gnimm/neuromime/1.0.1_minor_corrections_post_MUTEK/sketches_notes/oldboard.jpg

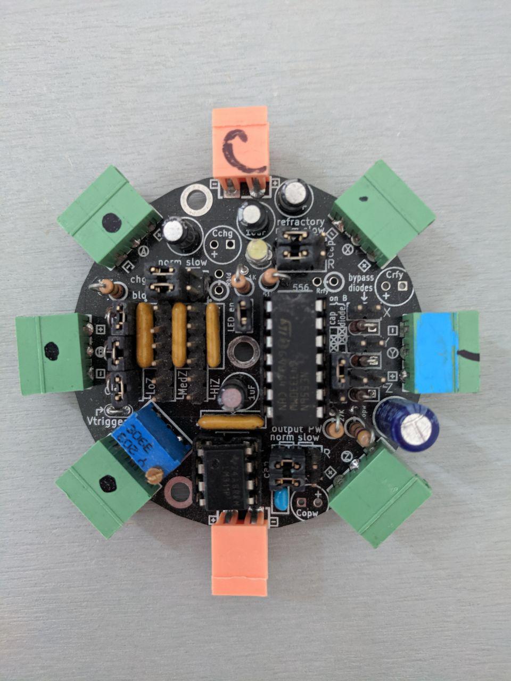
1.0.1_minor_corrections_post_MUTEK/sketches_notes/oldboard.jpg
