gnimm/neuromime/1.0.1_minor_corrections_post_MUTEK/sketches_notes/signal-attachment.jpeg

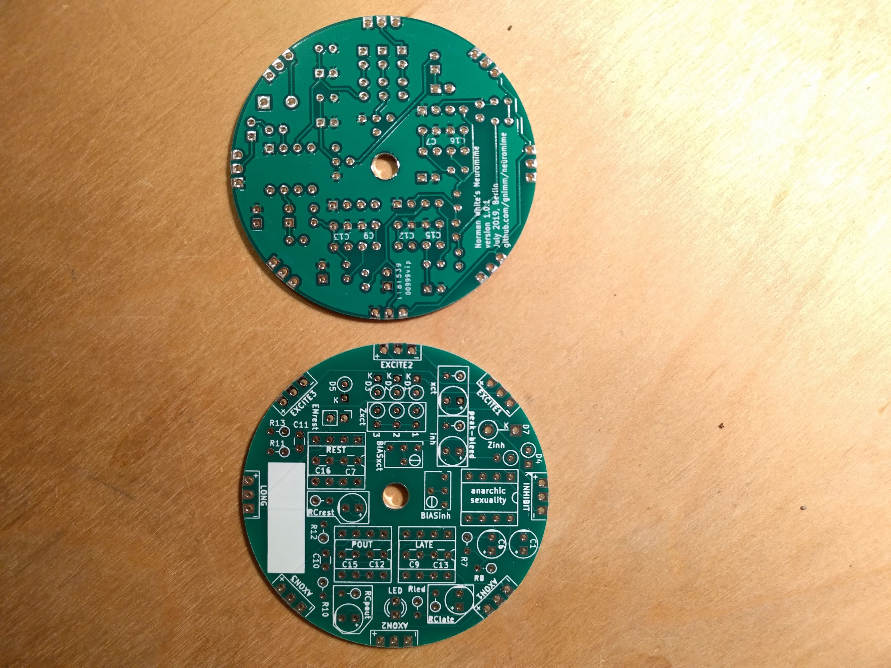
1.0.1_minor_corrections_post_MUTEK/sketches_notes/signal-attachment.jpeg
