gnimm/neuromime/ref/Neuromime_finished_board_ver_1.0.0.png

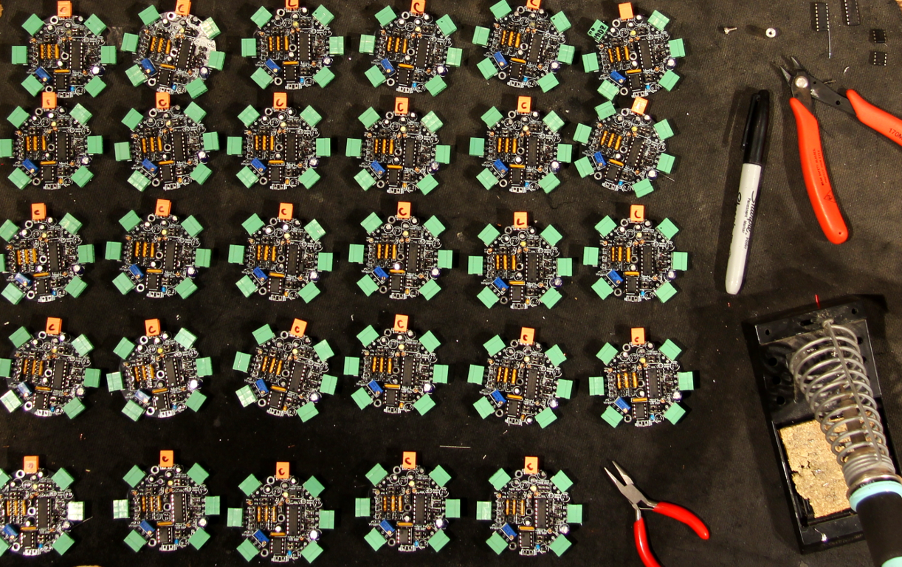
ref/Neuromime_finished_board_ver_1.0.0.png
