gnimm/neuromime/1.0.1/project_files/neuromime_1.0.1.sch

## KiCad design 1.0.1/project_files/neuromime_1.0.1.sch (2019-07-09)

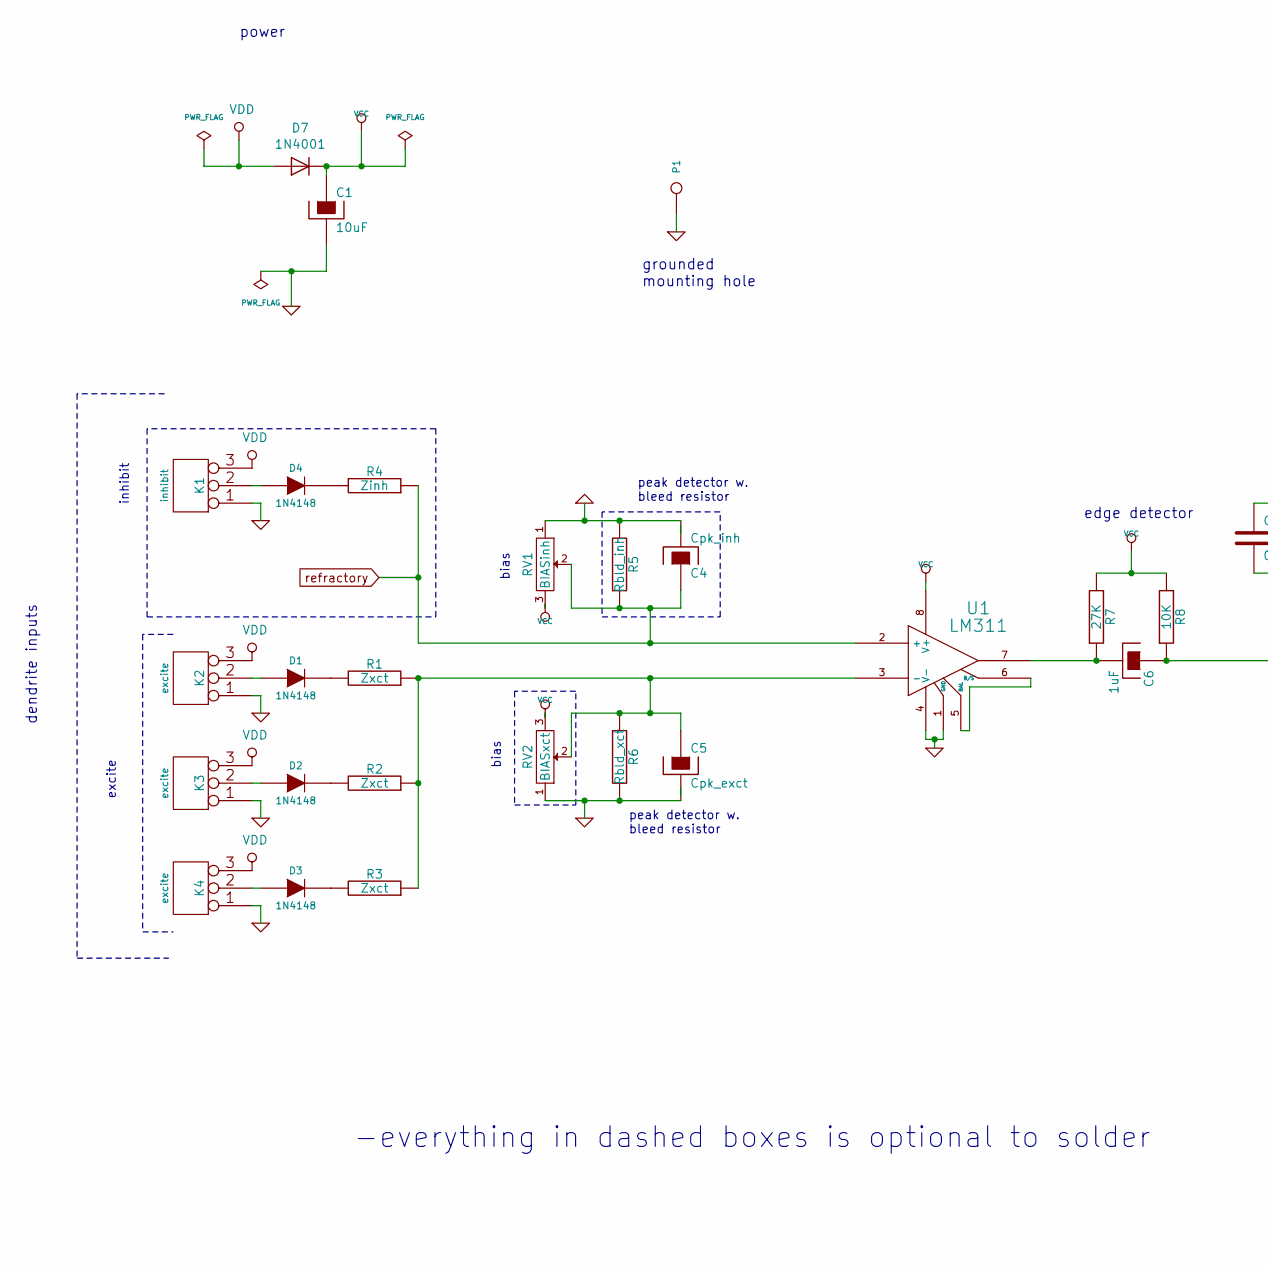
[picture p19: schematic neuromime_1.0.1.sch, part in row 1, column 1]

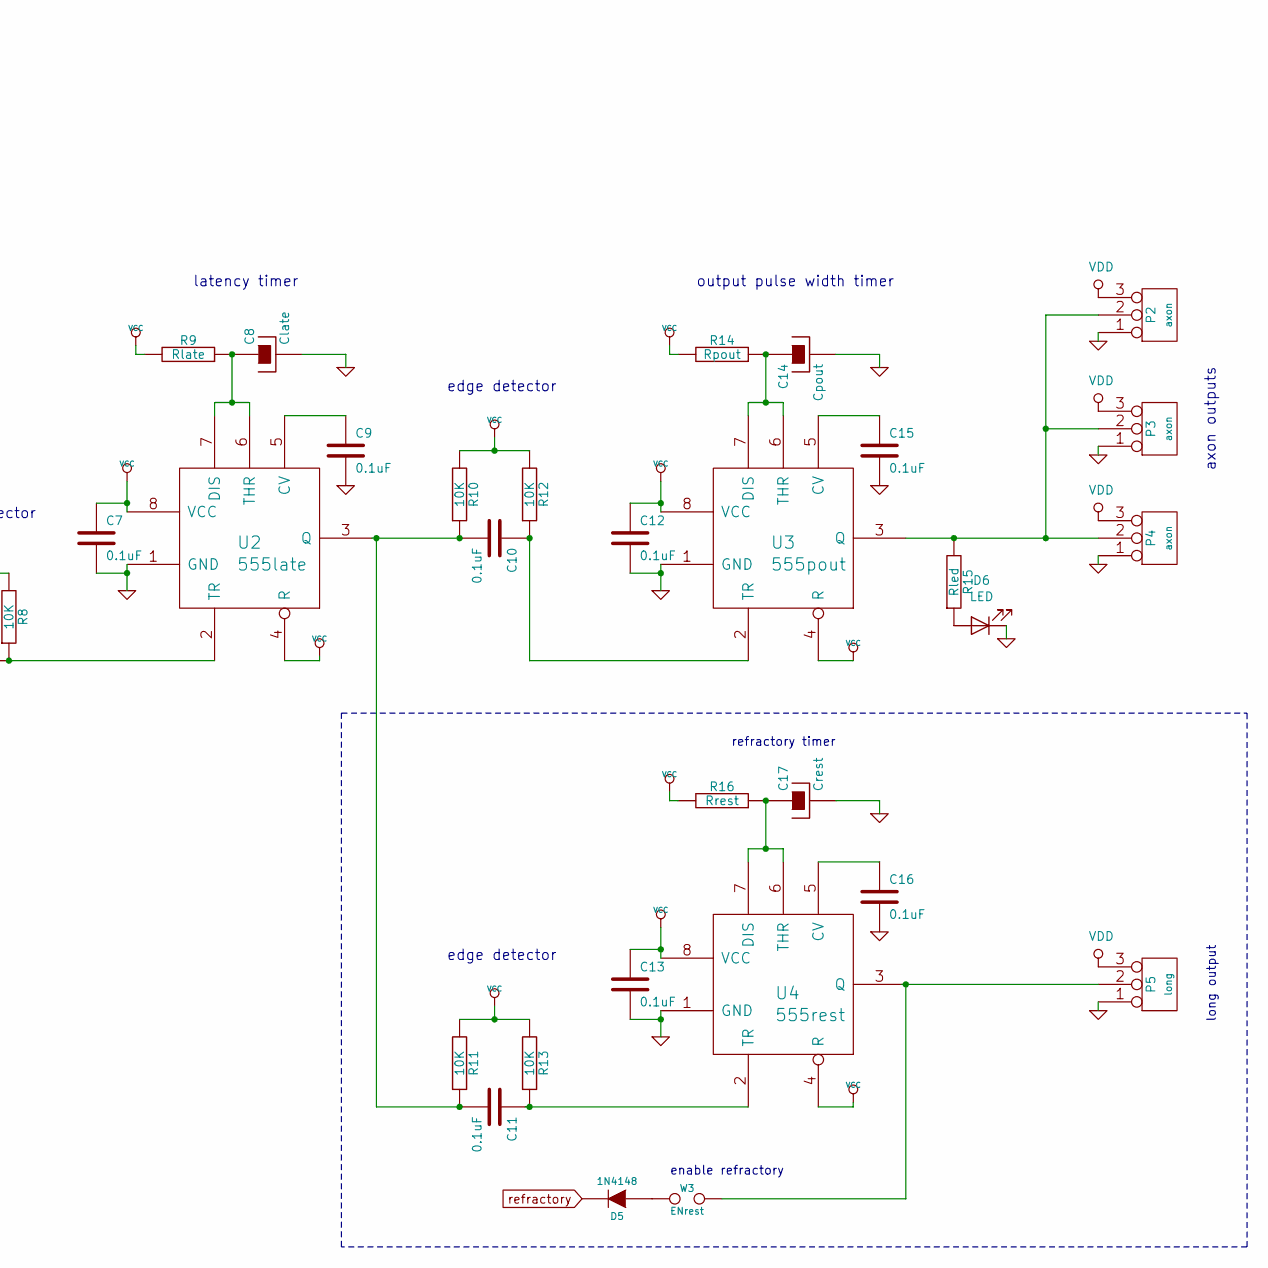
[picture p20: schematic neuromime_1.0.1.sch, part in row 1, column 2]

Parts:
C1: 10uF; CP_Radial_D5.0mm_P2.50mm_positive_symbol_inside
C4: Cpk_inh; CP_Radial_D5.0mm_P2.50mm_positive_symbol_inside
C5: Cpk_exct; CP_Radial_D5.0mm_P2.50mm_positive_symbol_inside
C6: 1uF; CP_Radial_D5.0mm_P2.50mm_positive_symbol_inside
C7, C9, C10, C11, C12, C13, C15, C16: 0.1uF; C_Disc_D3.0mm_W1.6mm_P2.50mm
C8: Clate; CP_Radial_D5.0mm_P2.50mm_positive_symbol_inside
C14: Cpout; CP_Radial_D5.0mm_P2.50mm_positive_symbol_inside_single_corr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
C17: Crest; CP_Radial_D5.0mm_P2.50mm_positive_symbol_inside
D1, D2, D3, D4, D5: 1N4148; D_DO-35_SOD27_P2.54mm_Vertical_KathodeUp
D6: LED; LED_D3.0mm
D7: 1N4001; D_DO-41_SOD81_P5.08mm_Vertical_KathodeUp
K1: inhibit; PinSocket_1x03_P2.54mm_Horizontal_elongated
K2, K3, K4: excite; PinSocket_1x03_P2.54mm_Horizontal_elongated
P1: mnt; MountingHole_4.5mm_PTH
P2, P3, P4: axon; PinHeader_1x03_P2.54mm_Horizontal_elomgated_pads
P5: long; PinHeader_1x03_P2.54mm_Horizontal_elomgated_pads
R1, R2, R3: Zxct; R_Axial_DIN0207_L6.3mm_D2.5mm_P2.54mm_Vertical_pad_numbers_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
R4: Zinh; R_Axial_DIN0207_L6.3mm_D2.5mm_P2.54mm_Vertical_pad_numbers_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
R5: Rbld_inh; R_Axial_DIN0204_L3.6mm_D1.6mm_P2.54mm_Vertical
R6: Rbld_xct; R_Axial_DIN0204_L3.6mm_D1.6mm_P2.54mm_Vertical
R7: 27K; R_Axial_DIN0204_L3.6mm_D1.6mm_P2.54mm_Vertical
R8, R10, R11, R12, R13: 10K; R_Axial_DIN0204_L3.6mm_D1.6mm_P2.54mm_Vertical
R9: Rlate; R_Axial_DIN0204_L3.6mm_D1.6mm_P2.54mm_Vertical
R14: Rpout; R_Axial_DIN0204_L3.6mm_D1.6mm_P2.54mm_Vertical
R15: Rled; R_Axial_DIN0204_L3.6mm_D1.6mm_P2.54mm_Vertical
R16: Rrest; R_Axial_DIN0204_L3.6mm_D1.6mm_P2.54mm_Vertical
RV1: BIASinh; Potentiometer_Bourns_3266W_Vertical_pin_variation
RV2: BIASxct; Potentiometer_Bourns_3266W_Vertical_pin_variation
U1: LM311; DIP-8_W7.62mm_Socket
U2: 555late; DIP-8_W7.62mm_Socket
U3: 555pout; DIP-8_W7.62mm_Socket
U4: 555rest; DIP-8_W7.62mm_Socket
W3: ENrest; PinHeader_1x02_P2.54mm_Vertical

Connections:
GND: C1.2, C4.2, C5.2, C7.2, C8.2, C9.2, C12.2, C13.2, C14.2, C15.2, C16.2, C17.2, D6.1 (K), K1.1, K2.1, K3.1, K4.1, P1.1, P2.1, P3.1, P4.1, P5.1, R5.2, R6.2, RV1.1, RV2.1, U1.1 (GND), U1.4 (V-), U2.1 (GND), U3.1 (GND), U4.1 (GND)
unnamed: C5.1, R1.1, R2.1, R3.1, R6.1, RV2.2, U1.3 (-)
unnamed: C6.1, R8.1, U2.2 (TR)
unnamed: C6.2, R7.1, U1.7
unnamed: C8.1, R9.1, U2.6 (THR), U2.7 (DIS)
unnamed: C9.1, U2.5 (CV)
unnamed: C10.1, R12.1, U3.2 (TR)
unnamed: C10.2, C11.2, R10.1, R11.1, U2.3 (Q)
unnamed: C11.1, R13.1, U4.2 (TR)
unnamed: C14.1, R14.1, U3.6 (THR), U3.7 (DIS)
unnamed: C15.1, U3.5 (CV)
unnamed: C16.1, U4.5 (CV)
unnamed: C17.1, R16.1, U4.6 (THR), U4.7 (DIS)
unnamed: D1.1 (A), K2.2 (PM)
unnamed: D1.2 (K), R1.2
unnamed: D2.1 (A), K3.2 (PM)
unnamed: D2.2 (K), R2.2
unnamed: D3.1 (A), K4.2 (PM)
unnamed: D3.2 (K), R3.2
unnamed: D4.1 (A), K1.2 (PM)
unnamed: D4.2 (K), R4.2
unnamed: D5.1 (A), W3.1
unnamed: D6.2 (A), R15.1
unnamed: P2.2 (PM), P3.2 (PM), P4.2 (PM), R15.2, U3.3 (Q)
unnamed: P5.2 (PM), U4.3 (Q), W3.2
unnamed: U1.5 (BAL), U1.6 (B/S)
VCC: C1.1, C7.1, C12.1, C13.1, D7.1 (K), R7.2, R8.2, R9.2, R10.2, R11.2, R12.2, R13.2, R14.2, R16.2, RV1.3, RV2.3, U1.8 (V+), U2.4 (R), U2.8 (VCC), U3.4 (R), U3.8 (VCC), U4.4 (R), U4.8 (VCC)
VDD: D7.2 (A), K1.3, K2.3, K3.3, K4.3, P2.3, P3.3, P4.3, P5.3
refractory: C4.1, D5.2 (K), R4.1, R5.1, RV1.2, U1.2 (+)

Notes on the sheet:
grounded mounting hole
dendrite inputs
axon outputs
power
edge detector
output pulse width timer
latency timer
inhibit
excite
bias
peak detector w. bleed resistor
enable refractory
refractory timer
long output
-everything in dashed boxes is optional to solder
