gnimm/neuromime/1.0.0/project_files/rescue-backup/neuromime_1.0.0-2019-07-08-18-24-22.sch

## KiCad design 1.0.0/project_files/rescue-backup/neuromime_1.0.0-2019-07-08-18-24-22.sch (2015-03-06)

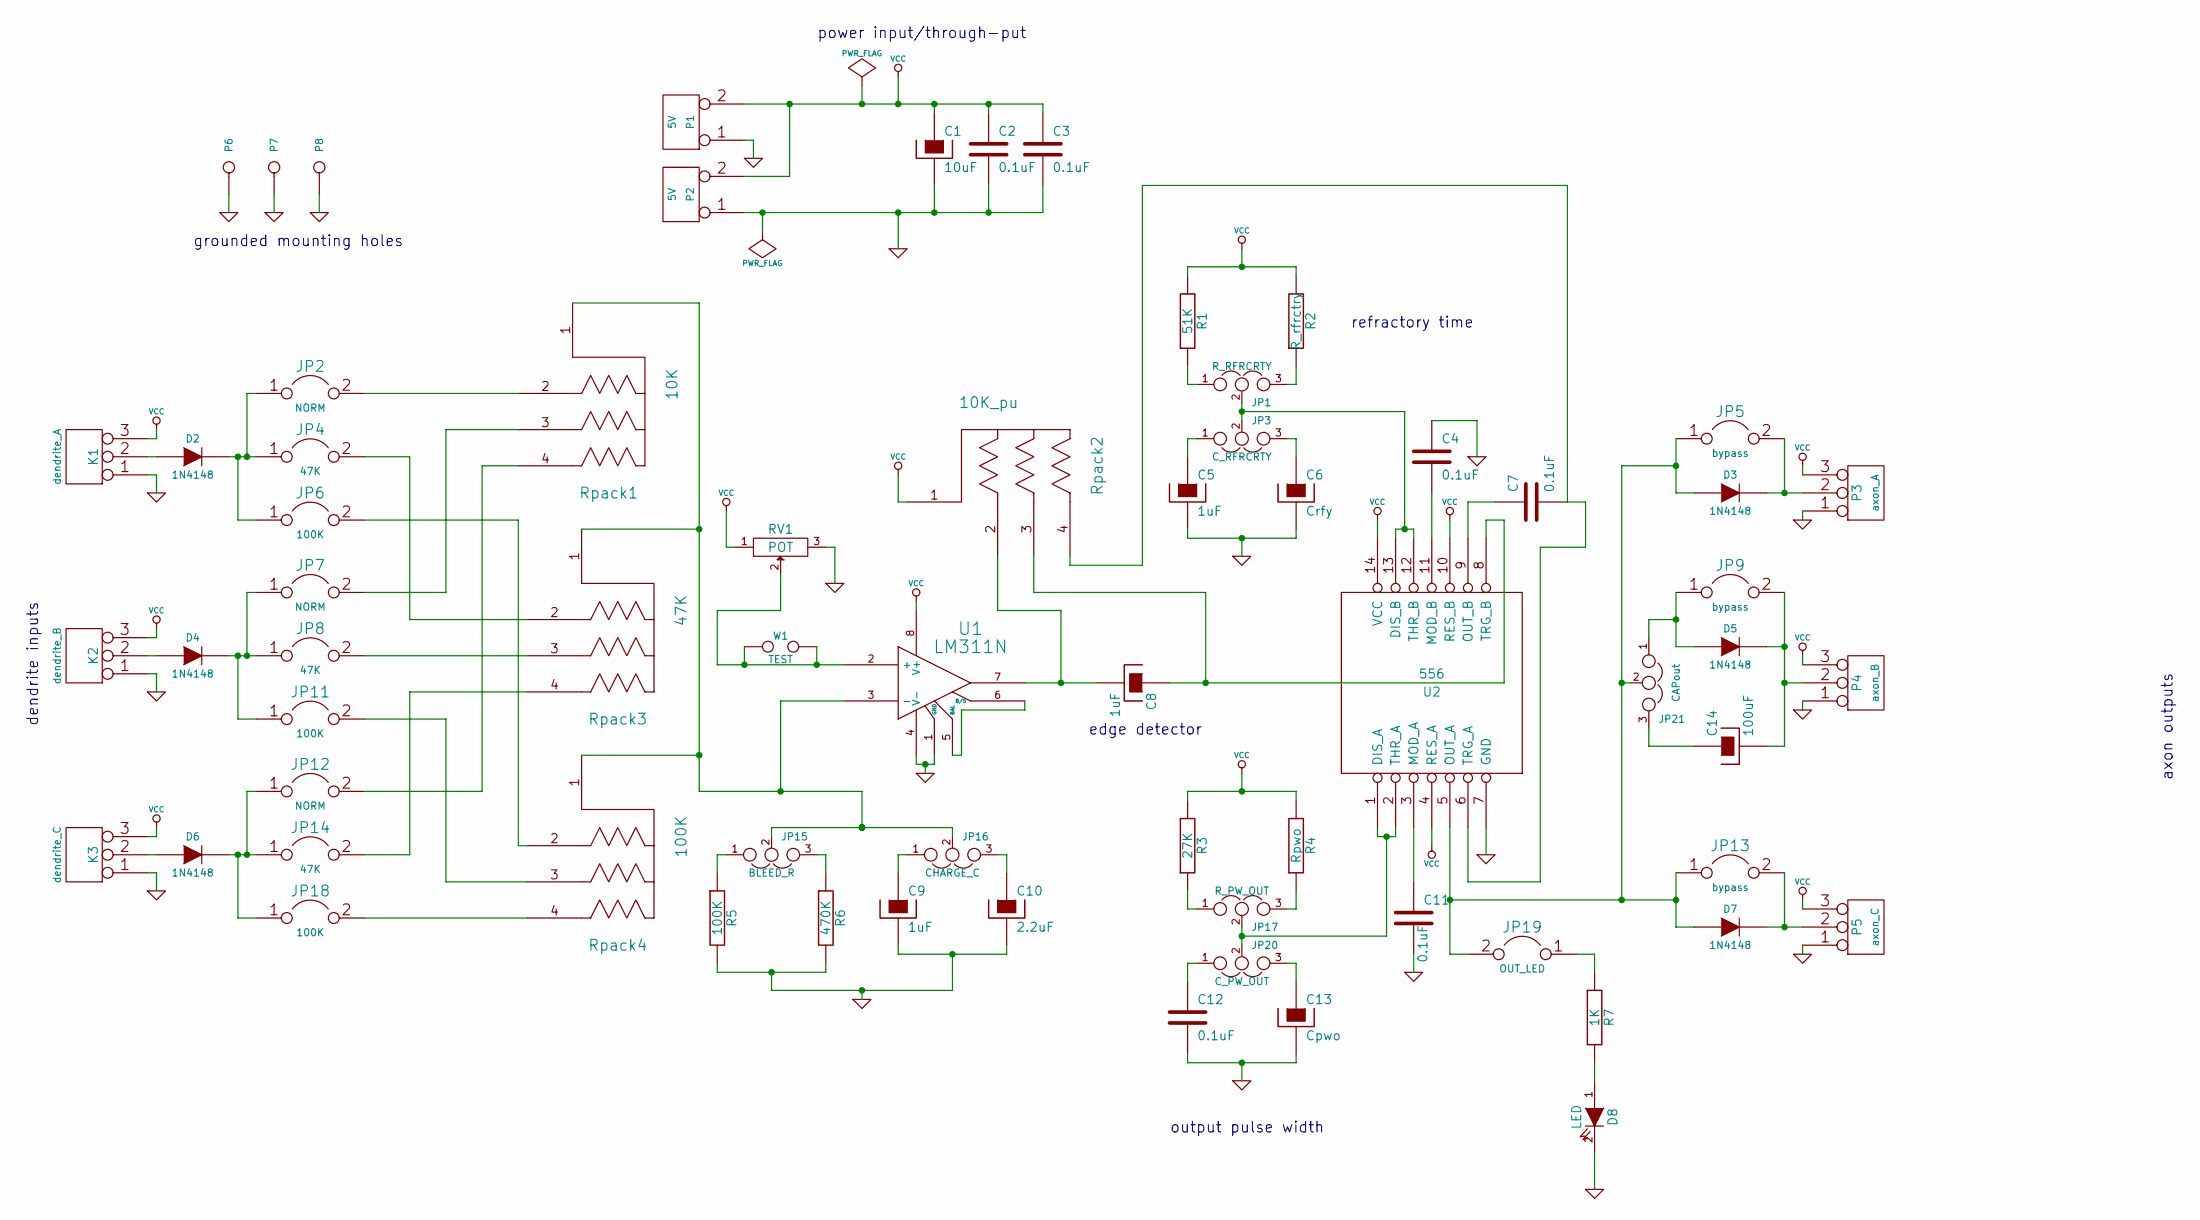
[picture p21: schematic neuromime_1.0.0-2019-07-08-18-24-22.sch]

Parts:
C1: 10uF
C2, C3, C4, C7, C11, C12: 0.1uF
C5, C8, C9: 1uF
C6: Crfy
C10: 2.2uF
C13: Cpwo
C14: 100uF
D2, D3, D4, D5, D6, D7: 1N4148
D8: LED
JP1: R_RFRCRTY
JP2, JP7, JP12: NORM
JP3: C_RFRCRTY
JP4, JP8, JP14: 47K
JP5, JP9, JP13: bypass
JP6, JP11, JP18: 100K
JP15: BLEED_R
JP16: CHARGE_C
JP17: R_PW_OUT
JP19: OUT_LED
JP20: C_PW_OUT
JP21: CAPout
K1: dendrite_A
K2: dendrite_B
K3: dendrite_C
P1, P2: 5V
P3: axon_A
P4: axon_B
P5: axon_C
P6, P7, P8: CONN_1
R1: 51K
R2: R_rfrctry
R3: 27K
R4: Rpwo
R5: 100K
R6: 470K
R7: 1K
RV1: POT
Rpack1: 10K
Rpack2: 10K_pu
Rpack3: 47K
Rpack4: 100K
U1: LM311N
U2: 556
W1: TEST

Connections:
GND: C1.2, C2.2, C3.2, C4.1, C5.2, C6.2, C9.2, C10.2, C11.2, C12.2, C13.2, D8.2 (K), K1.1, K2.1, K3.1, P1.1, P2.1, P3.1, P4.1, P5.1, P6.1, P7.1, P8.1, R5.2, R6.2, RV1.3, U1.1 (GND), U1.4 (V-), U2.7 (GND)
unnamed: C4.2, U2.11 (MOD_B)
unnamed: C5.1, JP3.1
unnamed: C6.1, JP3.3
unnamed: C7.1, U2.9 (OUT_B)
unnamed: C7.2, Rpack2.4, U2.6 (TRG_A)
unnamed: C8.1, Rpack2.3, U2.8 (TRG_B)
unnamed: C8.2, Rpack2.2, U1.7
unnamed: C9.1, JP16.1
unnamed: C10.1, JP16.3
unnamed: C11.1, U2.3 (MOD_A)
unnamed: C12.1, JP20.1
unnamed: C13.1, JP20.3
unnamed: C14.1, JP21.3
unnamed: C14.2, D5.2 (K), JP9.2, P4.2 (PM)
unnamed: D2.1 (A), K1.2 (PM)
unnamed: D2.2 (K), JP2.1, JP4.1, JP6.1
unnamed: D3.1 (A), D7.1 (A), JP5.1, JP13.1, JP19.2, JP21.2, U2.5 (OUT_A)
unnamed: D3.2 (K), JP5.2, P3.2 (PM)
unnamed: D4.1 (A), K2.2 (PM)
unnamed: D4.2 (K), JP7.1, JP8.1, JP11.1
unnamed: D5.1 (A), JP9.1, JP21.1
unnamed: D6.1 (A), K3.2 (PM)
unnamed: D6.2 (K), JP12.1, JP14.1, JP18.1
unnamed: D7.2 (K), JP13.2, P5.2 (PM)
unnamed: D8.1 (A), R7.2
unnamed: JP1.1, R1.1
unnamed: JP1.2, JP3.2, U2.12 (THR_B), U2.13 (DIS_B)
unnamed: JP1.3, R2.1
unnamed: JP2.2, Rpack1.2
unnamed: JP4.2, Rpack3.2
unnamed: JP6.2, Rpack4.2
unnamed: JP7.2, Rpack1.3
unnamed: JP8.2, Rpack3.3
unnamed: JP11.2, Rpack4.3
unnamed: JP12.2, Rpack1.4
unnamed: JP14.2, Rpack3.4
unnamed: JP15.1, R5.1
unnamed: JP15.2, JP16.2, Rpack1.1, Rpack3.1, Rpack4.1, U1.3 (-)
unnamed: JP15.3, R6.1
unnamed: JP17.1, R3.1
unnamed: JP17.2, JP20.2, U2.1 (DIS_A), U2.2 (THR_A)
unnamed: JP17.3, R4.1
unnamed: JP18.2, Rpack4.4
unnamed: JP19.1, R7.1
unnamed: RV1.2, U1.2 (+), W1.1, W1.2
unnamed: U1.5 (BAL), U1.6 (B/S)
VCC: C1.1, C2.1, C3.1, K1.3, K2.3, K3.3, P1.2 (PM), P2.2 (PM), P3.3, P4.3, P5.3, R1.2, R2.2, R3.2, R4.2, RV1.1, Rpack2.1, U1.8 (V+), U2.4 (RES_A), U2.10 (RES_B), U2.14 (VCC)

Notes on the sheet:
grounded mounting holes
dendrite inputs
axon outputs
power input/through-put
edge detector
output pulse width
refractory time
